Ubiqu0/UbiOne/examples/drone/v_radio/connect_vGPS.py

import asyncio
import time,logging,json
import serial
import sys
sys.path.insert(0, '/home/pi/Ubiquo')
from ubirtc.webrtc import WebRTC,GSTWebRTCApp
from yamspy_async import MSPy
import pynmea2
from pynmea2 import dm_to_sd
import aioserial

WS_SERVER = 'wss://ubiquo.net/ws/control/'
DEVICE_ID = '' #insert your device ID
SERIAL_UBIONE = "/dev/serial0"

SERIAL_LTE = aioserial.AioSerial("/dev/ttyUSB1", baudrate = 115200, timeout = 0.5,rtscts=True, dsrdtr=True)

class GstApp(GSTWebRTCApp):
    def __init__(self, board,*args, **kwargs):
        super().__init__(*args, **kwargs)
        self.board = board
        self.last_msg_received = time.time()
        self.received_cmd = False


GPS_LOOP_TIME = 0.1
async def send_GPS_data(ser,gst_app):

    turn on GPS
    await ser.write_async('AT+QGPS=1\r'.encode())

    #declare GPS values with dummy
    fix = 0
    num_sats = 1
    lat = 1
    lon = 1
    altitude = 1
    spd_over_grnd = 1

    while 1:
        await asyncio.sleep(GPS_LOOP_TIME)
        data = await ser.readline_async()
        data = data.decode("utf-8")
        # data = ser.readline().decode("utf-8")
        if data[0:6] == "$GPRMC":
            try:
                msg = pynmea2.parse(data)
                spd_over_grnd = int(float(msg.spd_over_grnd)*51.44)
                # spd_over_grnd = int(float(1)*51.44)
                # true_course = int(float(msg.true_course)*10)
            except pynmea2.nmea.ChecksumError:
                continue
        elif data[0:6] == "$GPGGA":
                msg = pynmea2.parse(data)
                num_sats = int(msg.num_sats)
                lat= int(dm_to_sd(msg.lat)*10000000)
                lon = int(dm_to_sd(msg.lon)*10000000)
                altitude = int(msg.altitude)
                fix = int(msg.gps_qual)

        data_gps = gst_app.board.convert([fix], 8)
        data_gps += gst_app.board.convert([num_sats], 8)
        data_gps += gst_app.board.convert([lat], 32)
        data_gps += gst_app.board.convert([lon], 32)
        data_gps += gst_app.board.convert([altitude], 16)
        data_gps += gst_app.board.convert([spd_over_grnd], 16)

        # Send GPS data
        if await gst_app.board.send_RAW_msg(MSPy.MSPCodes['MSP_SET_RAW_GPS'], data=data_gps):
            # print("data sent!")
            dataHandler = await gst_app.board.receive_msg()
            # print("data received!",dataHandler)
            await gst_app.board.process_recv_data(dataHandler)
            # print("data processed!")

        # # Ask GPS data
        if await gst_app.board.send_RAW_msg(MSPy.MSPCodes['MSP_RAW_GPS'], data=[]):
            # print("data sent!")
            dataHandler = await gst_app.board.receive_msg()
            await gst_app.board.process_recv_data(dataHandler)
            # print("data processed!",dataHandler)
            # print(gst_app.board.GPS_DATA)



SEND_TIME_INTERVAL = 1
async def send_data_message(gst_app):
    count = 0

    while True:
        await asyncio.sleep(SEND_TIME_INTERVAL)
        if gst_app.is_data_channel_ready():
            ###########################
            ######## add your code here
            #########################
            # send dictionary with t1,t2,...,t8 as keys and the respective value with the format ['name',value]
            # If you want a progressive bar you can send the min and max with ['name',value,min,max]

            armed = gst_app.board.bit_check(gst_app.board.CONFIG['mode'],0)
            flags = gst_app.board.process_armingDisableFlags(gst_app.board.CONFIG['armingDisableFlags'])
            await gst_app.board.fast_read_altitude()
            await gst_app.board.fast_read_analog()
            altitude = gst_app.board.SENSOR_DATA['altitude']
            voltage = gst_app.board.ANALOG['voltage']

            flags= ','.join(flags)
            check_status_time = time.time()
            print(armed,flags,str(gst_app.board.GPS_DATA['lat']),type(gst_app.board.GPS_DATA['lat']))

            data = {
                't1':['ARMED',1 if armed else 0,0,1],
                't2':['Flags',flags],
                't3':['altitude',altitude,0,100],
                't4':['voltage',voltage],
                # 't5':['lat',100],
                't5':['lat',gst_app.board.GPS_DATA['lat']],
                't6':['lon',gst_app.board.GPS_DATA['lon']],

                }
            count+=1

            gst_app.send_data_message('telemetry',data)



async def run():

    pipeline_str  = ''' webrtcbin name=sendrecv bundle-policy=max-bundle
    v4l2src device=/dev/video0 !
    video/x-h264,profile=constrained-baseline,width=640,height=360,level=3.0,framerate=30/1 !
    queue max-size-time=100000000 ! h264parse !
    rtph264pay mtu=1024 config-interval=-1 name=payloader !
    capssetter caps=\"application/x-rtp,profile-level-id=42c028,encoding-name=H264,payload=96\" ! sendrecv.'''

    async with MSPy(device=SERIAL_UBIONE, logfilename=None, loglevel = 'WARNING',baudrate=115200)as ubione:
        command_list = ['MSP_API_VERSION', 'MSP_FC_VARIANT', 'MSP_FC_VERSION', 'MSP_BUILD_INFO',
                        'MSP_BOARD_INFO', 'MSP_UID', 'MSP_ACC_TRIM', 'MSP_NAME', 'MSP_STATUS',
                        'MSP_STATUS_EX','MSP_BATTERY_CONFIG', 'MSP_BATTERY_STATE', 'MSP_BOXNAMES']
        for msg in command_list:
            if await ubione.send_RAW_msg(MSPy.MSPCodes[msg], data=[]):
                dataHandler = await ubione.receive_msg()
                await ubione.process_recv_data(dataHandler)

        webrct_connection = WebRTC(
                                DEVICE_ID,
                                WS_SERVER,
                                app = GstApp(board = ubione,audio = False, pipeline_str = pipeline_str)
                            )
        asyncio.ensure_future(send_data_message(webrct_connection.app))
        asyncio.ensure_future(send_GPS_data(SERIAL_LTE,webrct_connection.app))

        await webrct_connection.connect()
        await webrct_connection.start()


if __name__ == "__main__":
    #start GPS

    try:
        loop = asyncio.get_event_loop()
        loop.run_until_complete(run())
        loop.close()
    except Exception as e:
        print("Caught exception: %s" % e)
